Socketto/Incubator_ESP32/arduino/Incubator_ESP32/ntc.ino

// NTC B3950 Thermistor
// the formula for temp in kelvin is
//                 1
// T = ----------------------------
//     1/To + (1/beta) * ln(Rt/Ro)
//
// https://en.wikipedia.org/wiki/Thermistor

// ESP32 ADC non-liear issue
// https://www.esp32.com/viewtopic.php?t=1045
// https://github.com/espressif/esp-idf/issues/164
// https://docs.espressif.com/projects/esp-idf/en/latest/api-reference/peripherals/adc.html#adc-calibration

int ThermistorPin = 35;
int ThermistorPinEXT = 34;
double adcMax = 4095, Vs = 3.3;

double R1 = 10000.0;   // voltage divider resistor value
double Beta = 3950.0;  // Beta value
double To = 298.15;    // Temperature in Kelvin for 25 degree Celsius
double Ro = 10000.0;   // Resistance of Thermistor at 25 degree Celsius



const float ADC_LUT[4096] = { 0,
                              80.2000, 81.2000, 82.4000, 83.6000, 84.6000, 85.8000, 86.8000, 87.8000, 88.8000, 89.8000, 91.0000, 92.0000, 93.0000, 94.0000, 95.0000,
                              96.2000, 97.8000, 99.0000, 100.2000, 101.8000, 103.0000, 104.4000, 105.8000, 107.0000, 108.4000, 109.8000, 111.0000, 112.4000, 113.4000, 114.4000,
                              115.4000, 116.2000, 117.2000, 118.2000, 119.2000, 120.2000, 121.2000, 122.2000, 123.2000, 124.0000, 125.0000, 126.0000, 127.0000, 128.0000, 129.4000,
                              130.8000, 131.8000, 133.0000, 134.2000, 135.8000, 136.8000, 138.0000, 139.2000, 140.6000, 141.8000, 143.0000, 144.0000, 145.8000, 147.0000, 148.8000,
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
  {
    Tc = lastRead;
  }
  else
  {
	lastRead = Tc;
  }
  return Tc+deltaTemperature;
}

static float lastExtReadTemp = 15;
bool FirstReadExtTemp = true;
double filteredTemp = 0;
double alpha = 0.1; // Regola la stabilità
double readtempEXT() {
  double Vout, Rt = 0;
  double T, Tc, Tf = 0;

  double adc = 0;
  adc = analogRead(ThermistorPinEXT);

  //double adc1 = 0;
  //adc1 = analogRead(34);

  adc = ADC_LUT[(int)adc];


  Vout = adc * Vs / adcMax;
  Rt = (R1 * Vout) / (Vs - Vout);

  T = 1 / (1 / To + log(Rt / Ro) / Beta);  // Temperature in Kelvin
  Tc = T - 273.15;                         // Celsius
  Tf = Tc * 9 / 5 + 32;                    // Fahrenheit
  //if (Tc > 0) Serial.println(Tc);
  
  if(isnan(Tc))
  {
    Tc = lastExtReadTemp;
  }
  else
  {
	  lastExtReadTemp = Tc;
  }

  if(FirstReadExtTemp)
  {
    FirstReadExtTemp = false;
    filteredTemp = Tc;
  }
  else
  {
    filteredTemp = alpha * Tc + (1 - alpha) * filteredTemp;  // Filtro
  }

  return filteredTemp;
}
