Socketto/Incubator_ESP32/arduino/Incubator_ESP32/logo.ino

#include <stdint.h>



static const uint16_t image_data_LOGO[20480] = {
  // ████████████████████████████████████████████████████████████████████████████████████████████████████████████████████████████████████████████████████████████████
  // █████████████████████████████████████████████████████████████████████████████████████████████████▓▓▓████████████████████████████████████████████████████████████
  // █████████████████████████████████████████████████████████████████████████████████████████████▒░∙░░░░░░∙░▓███████████████████████████████████████████████████████
  // ███████████████████████████████████████████████████████████████████████████████████████████▒∙░░░░░░░░░░░░∙░█████████████████████████████████████████████████████
  // ██████████████████████████████████████████████████████████████████████████████████████████∙░░▒▒▒▒▒▒▒▒▒▒▒▒░░░∙███████████████████████████████████████████████████
  // █████████████████████████████████████████████████████████████████████████████████████████∙░░▒▒▒▒▒▒▒▒▒▒▒▒▒▒▒░░░▒█████████████████████████████████████████████████
  // ████████████████████████████████████████████████████████████████████████████████████████░░░▒▒▒▒▒▒▒▒▒▒▒▒▒▒▒▒▒▒░░░████████████████████████████████████████████████
  // ████████████████████████████████████████████████████████████████████████████████████████░░▒▒▒▒▒▒▒▒▒▒▒▒▒▒▒▒▒▒▒▒░░▒███████████████████████████████████████████████
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
};
