Socketto/Incubator_ESP32/arduino/Incubator_ESP32/Images.ino

#include <stdint.h>


static const uint8_t image_data_heater[20] = {
  // ∙∙██∙∙∙██∙
  // ∙██∙∙∙██∙∙
  // ∙██∙∙∙██∙∙
  // ∙∙██∙∙∙██∙
  // ∙∙∙██∙∙∙██
  // ∙∙∙██∙∙∙██
  // ∙∙██∙∙∙██∙
  // ∙██∙∙∙██∙∙
  // ∙∙∙∙∙∙∙∙∙∙
  // ██████████
  0x31, 0x80,
  0x63, 0x00,
  0x63, 0x00,
  0x31, 0x80,
  0x18, 0xc0,
  0x18, 0xc0,
  0x31, 0x80,
  0x63, 0x00,
  0x00, 0x00,
  0xff, 0xc0
};

static const uint8_t image_data_humidifier[20] = {
  // ∙∙∙∙∙█∙∙∙∙
  // ∙∙∙∙∙█∙∙∙∙
  // ∙∙∙∙███∙∙∙
  // ∙∙∙∙███∙∙∙
  // ∙∙∙█████∙∙
  // ∙∙∙█████∙∙
  // ∙∙████∙██∙
  // ∙∙████∙██∙
  // ∙∙∙█████∙∙
  // ∙∙∙∙███∙∙∙
  0x04, 0x00,
  0x04, 0x00,
  0x0e, 0x00,
  0x0e, 0x00,
  0x1f, 0x00,
  0x1f, 0x00,
  0x3d, 0x80,
  0x3d, 0x80,
  0x1f, 0x00,
  0x0e, 0x00
};

static const uint8_t image_data_WIFI_WHITE[20] = {
  // ∙∙∙∙∙∙∙∙∙∙
  // ∙████████∙
  // ██∙∙∙∙∙∙██
  // █∙∙████∙∙█
  // ∙∙█∙∙∙∙█∙∙
  // ∙█∙∙██∙∙█∙
  // ∙∙∙█∙∙█∙∙∙
  // ∙∙∙∙∙∙∙∙∙∙
  // ∙∙∙∙██∙∙∙∙
  // ∙∙∙∙██∙∙∙∙
  0x00, 0x00,
  0x7f, 0x80,
  0xc0, 0xc0,
  0x9e, 0x40,
  0x21, 0x00,
  0x4c, 0x80,
  0x12, 0x00,
  0x00, 0x00,
  0x0c, 0x00,
  0x0c, 0x00
};

static const uint8_t image_data_WORLD_WHITE[20] = {
  // ∙∙∙████∙∙∙
  // ∙∙█∙██∙█∙∙
  // ∙██∙██∙██∙
  // █∙█∙██∙█∙█
  // ██████████
  // ██████████
  // █∙█∙██∙█∙█
  // ∙██∙██∙██∙
  // ∙∙█∙██∙█∙∙
  // ∙∙∙████∙∙∙
  0x1e, 0x00,
  0x2d, 0x00,
  0x6d, 0x80,
  0xad, 0x40,
  0xff, 0xc0,
  0xff, 0xc0,
  0xad, 0x40,
  0x6d, 0x80,
  0x2d, 0x00,
  0x1e, 0x00
};

static const uint8_t image_data_WIFI_WHITE_1[20] = {
  // ∙∙∙∙∙∙∙∙∙∙
  // ∙∙∙∙∙∙∙∙∙∙
  // ∙∙∙∙∙∙∙∙∙∙
  // ∙∙∙∙∙∙∙∙∙∙
  // ∙∙∙∙∙∙∙∙∙∙
  // ∙∙∙∙██∙∙∙∙
  // ∙∙∙█∙∙█∙∙∙
  // ∙∙∙∙∙∙∙∙∙∙
  // ∙∙∙∙██∙∙∙∙
  // ∙∙∙∙██∙∙∙∙
  0x00, 0x00,
  0x00, 0x00,
  0x00, 0x00,
  0x00, 0x00,
  0x00, 0x00,
  0x0c, 0x00,
  0x12, 0x00,
  0x00, 0x00,
  0x0c, 0x00,
  0x0c, 0x00
};

static const uint8_t image_data_WIFI_WHITE_0[20] = {
  // ∙∙∙∙∙∙∙∙∙∙
  // ∙∙∙∙∙∙∙∙∙∙
  // ∙∙∙∙∙∙∙∙∙∙
  // ∙∙∙∙∙∙∙∙∙∙
  // ∙∙∙∙∙∙∙∙∙∙
  // ∙∙∙∙∙∙∙∙∙∙
  // ∙∙∙∙∙∙∙∙∙∙
  // ∙∙∙∙∙∙∙∙∙∙
  // ∙∙∙∙██∙∙∙∙
  // ∙∙∙∙██∙∙∙∙
  0x00, 0x00,
  0x00, 0x00,
  0x00, 0x00,
  0x00, 0x00,
  0x00, 0x00,
  0x00, 0x00,
  0x00, 0x00,
  0x00, 0x00,
  0x0c, 0x00,
  0x0c, 0x00
};

static const uint8_t image_data_WIFI_WHITE_2[20] = {
  // ∙∙∙∙∙∙∙∙∙∙
  // ∙∙∙∙∙∙∙∙∙∙
  // ∙∙∙∙∙∙∙∙∙∙
  // ∙∙∙████∙∙∙
  // ∙∙█∙∙∙∙█∙∙
  // ∙█∙∙██∙∙█∙
  // ∙∙∙█∙∙█∙∙∙
  // ∙∙∙∙∙∙∙∙∙∙
  // ∙∙∙∙██∙∙∙∙
  // ∙∙∙∙██∙∙∙∙
  0x00, 0x00,
  0x00, 0x00,
  0x00, 0x00,
  0x1e, 0x00,
  0x21, 0x00,
  0x4c, 0x80,
  0x12, 0x00,
  0x00, 0x00,
  0x0c, 0x00,
  0x0c, 0x00
};
